Keyaan-07/RP2040-mini-SDR/images/18/bd.png

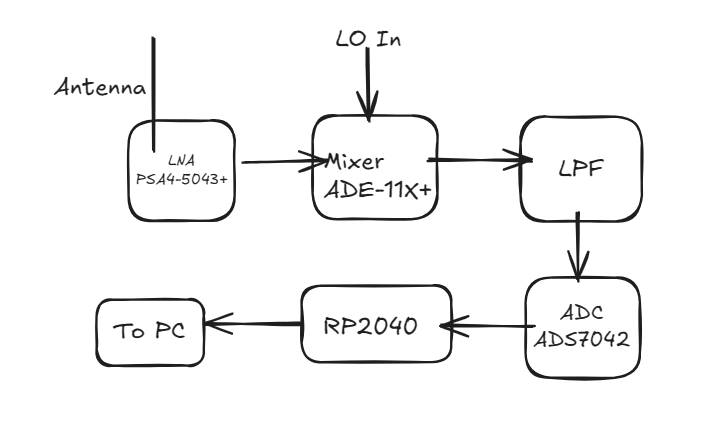
images/18/bd.png
